Raphael-Boichot/Game_Boy_Mini_Flashable_Camera/Images/Artifacts_with_22pf_C10.png

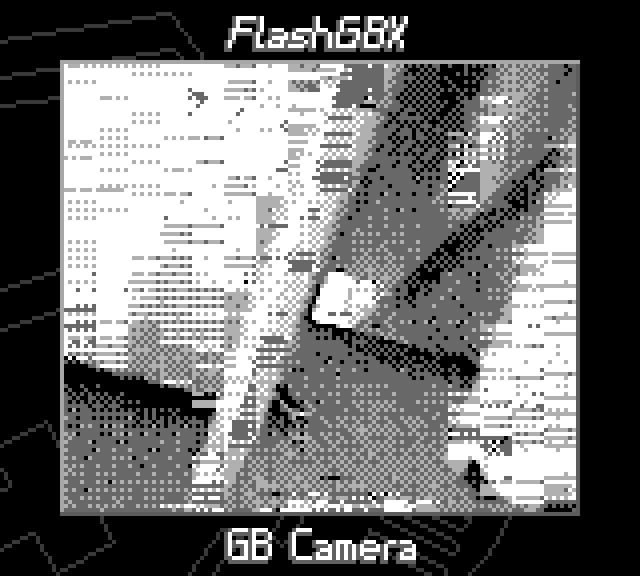
Images/Artifacts_with_22pf_C10.png
