Raphael-Boichot/Game_Boy_Mini_Flashable_Camera/PCB/GBC.kicad_sch

## KiCad design PCB/GBC.kicad_sch (2024-08-07)

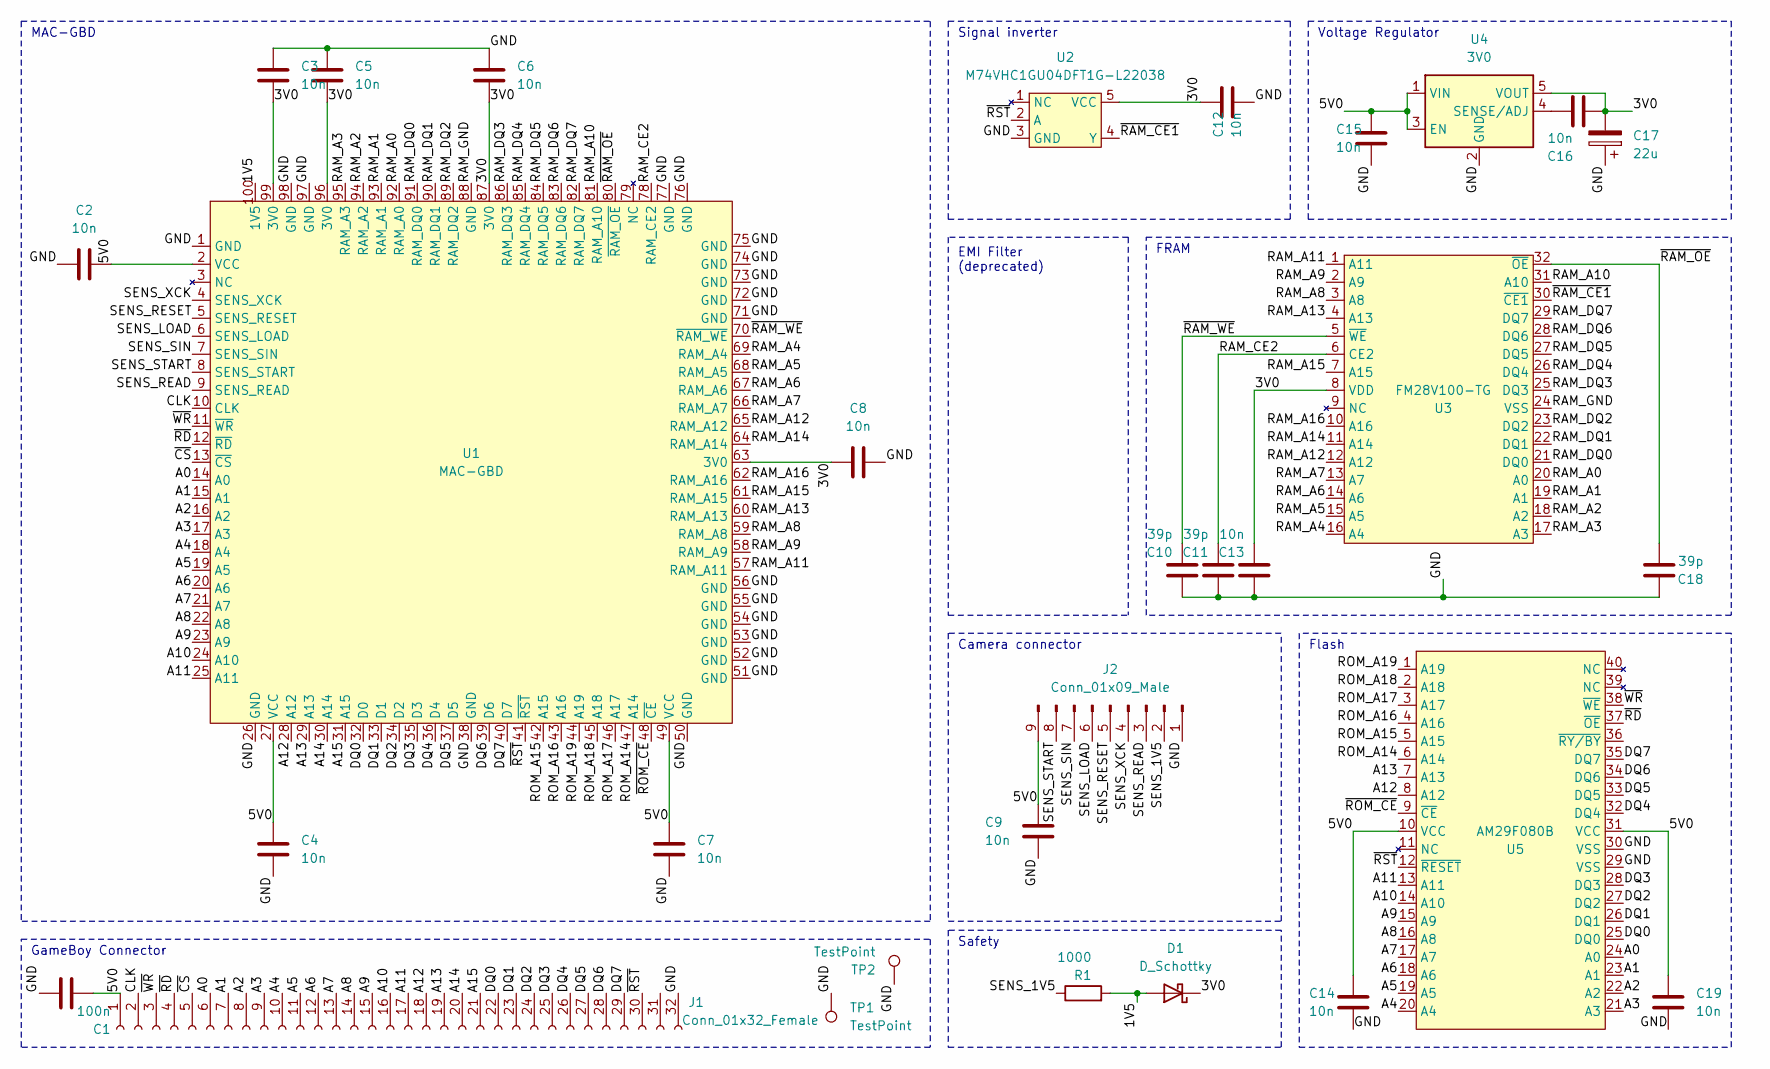
[picture p32: schematic GBC.kicad_sch]

Parts:
C1: 100n; C_0603_1608Metric
C2, C3, C4, C5, C6, C7, C8, C9, C12, C13, C14, C15, C16, C19: 10n; C_0603_1608Metric
C10, C11, C18: 39p; C_0603_1608Metric
C17: 22u; C_1206_3216Metric
D1: D_Schottky; Diode
J1: Conn_01x32_Female; Gamecart
J2: Conn_01x09_Male; JST_B9B-ZR-SM4-Flat
R1: 1000; R_0603_1608Metric
TP1, TP2: TestPoint; TestPoint_THTPad_D1.5mm_Drill0.7mm
U1: MAC-GBD; TQFP-100_14x14mm_P0.5mm
U2: M74VHC1GU04DFT1G-L22038; SC-88A
U3: FM28V100-TG; TSOP-I-32_12.4x8mm_P0.5mm
U4: 3V0; SOT-23-5_HandSoldering
U5: AM29F080B; TSOP-I-40_18.4x10mm_P0.5mm

Connections:
1V5: D1.2 (A), R1.2, U1.100 (1V5)
3V0: C3.1, C5.1, C6.1, C8.1, C12.1, C13.2, C16.2, C17.2, D1.1 (K), U1.63 (3V0), U1.87 (3V0), U1.96 (3V0), U1.99 (3V0), U2.5 (VCC), U3.8 (VDD), U4.5 (VOUT)
5V0: C1.1, C2.2, C4.1, C7.1, C9.2, C14.2, C15.1, C19.1, J1.1, J2.9, U1.2 (VCC), U1.27 (VCC), U1.49 (VCC), U4.1 (VIN), U4.3 (EN), U5.10 (VCC), U5.31 (VCC)
A0: J1.6, U1.14 (A0), U5.24 (A0)
A1: J1.7, U1.15 (A1), U5.23 (A1)
A2: J1.8, U1.16 (A2), U5.22 (A2)
A3: J1.9, U1.17 (A3), U5.21 (A3)
A4: J1.10, U1.18 (A4), U5.20 (A4)
A5: J1.11, U1.19 (A5), U5.19 (A5)
A6: J1.12, U1.20 (A6), U5.18 (A6)
A7: J1.13, U1.21 (A7), U5.17 (A7)
A8: J1.14, U1.22 (A8), U5.16 (A8)
A9: J1.15, U1.23 (A9), U5.15 (A9)
A10: J1.16, U1.24 (A10), U5.14 (A10)
A11: J1.17, U1.25 (A11), U5.13 (A11)
A12: J1.18, U1.28 (A12), U5.8 (A12)
A13: J1.19, U1.29 (A13), U5.7 (A13)
A14: J1.20, U1.30 (A14)
A15: J1.21, U1.31 (A15)
CLK: J1.2, U1.10 (CLK)
DQ0: J1.22, U1.32 (D0), U5.25 (DQ0)
DQ1: J1.23, U1.33 (D1), U5.26 (DQ1)
DQ2: J1.24, U1.34 (D2), U5.27 (DQ2)
DQ3: J1.25, U1.35 (D3), U5.28 (DQ3)
DQ4: J1.26, U1.36 (D4), U5.32 (DQ4)
DQ5: J1.27, U1.37 (D5), U5.33 (DQ5)
DQ6: J1.28, U1.39 (D6), U5.34 (DQ6)
DQ7: J1.29, U1.40 (D7), U5.35 (DQ7)
GND: C1.2, C2.1, C3.2, C4.2, C5.2, C6.2, C7.2, C8.2, C9.1, C10.1, C11.1, C12.2, C13.1, C14.1, C15.2, C17.1, C18.1, C19.2, J1.32, J2.1, TP1.1, TP2.1, U1.1 (GND), U1.26 (GND), U1.38 (GND), U1.50 (GND), U1.51 (GND), U1.52 (GND), U1.53 (GND), U1.54 (GND), U1.55 (GND), U1.56 (GND), U1.71 (GND), U1.72 (GND), U1.73 (GND), U1.74 (GND), U1.75 (GND), U1.76 (GND), U1.77 (GND), U1.97 (GND), U1.98 (GND), U2.3 (GND), U4.2 (GND), U5.29 (VSS), U5.30 (VSS)
unnamed: C16.1, U4.4 (SENSE/ADJ)
RAM_A0: U1.92 (RAM_A0), U3.20 (A0)
RAM_A1: U1.93 (RAM_A1), U3.19 (A1)
RAM_A2: U1.94 (RAM_A2), U3.18 (A2)
RAM_A3: U1.95 (RAM_A3), U3.17 (A3)
RAM_A4: U1.69 (RAM_A4), U3.16 (A4)
RAM_A5: U1.68 (RAM_A5), U3.15 (A5)
RAM_A6: U1.67 (RAM_A6), U3.14 (A6)
RAM_A7: U1.66 (RAM_A7), U3.13 (A7)
RAM_A8: U1.59 (RAM_A8), U3.3 (A8)
RAM_A9: U1.58 (RAM_A9), U3.2 (A9)
RAM_A10: U1.81 (RAM_A10), U3.31 (A10)
RAM_A11: U1.57 (RAM_A11), U3.1 (A11)
RAM_A12: U1.65 (RAM_A12), U3.12 (A12)
RAM_A13: U1.60 (RAM_A13), U3.4 (A13)
RAM_A14: U1.64 (RAM_A14), U3.11 (A14)
RAM_A15: U1.61 (RAM_A15), U3.7 (A15)
RAM_A16: U1.62 (RAM_A16), U3.10 (A16)
RAM_CE2: C11.2, U1.78 (RAM_CE2), U3.6 (CE2)
RAM_DQ0: U1.91 (RAM_DQ0), U3.21 (DQ0)
RAM_DQ1: U1.90 (RAM_DQ1), U3.22 (DQ1)
RAM_DQ2: U1.89 (RAM_DQ2), U3.23 (DQ2)
RAM_DQ3: U1.86 (RAM_DQ3), U3.25 (DQ3)
RAM_DQ4: U1.85 (RAM_DQ4), U3.26 (DQ4)
RAM_DQ5: U1.84 (RAM_DQ5), U3.27 (DQ5)
RAM_DQ6: U1.83 (RAM_DQ6), U3.28 (DQ6)
RAM_DQ7: U1.82 (RAM_DQ7), U3.29 (DQ7)
RAM_GND: U1.88 (GND), U3.24 (VSS)
ROM_A14: U1.47 (A14), U5.6 (A14)
ROM_A15: U1.42 (A15), U5.5 (A15)
ROM_A16: U1.43 (A16), U5.4 (A16)
ROM_A17: U1.46 (A17), U5.3 (A17)
ROM_A18: U1.45 (A18), U5.2 (A18)
ROM_A19: U1.44 (A19), U5.1 (A19)
SENS_1V5: J2.2, R1.1
SENS_LOAD: J2.6, U1.6 (SENS_LOAD)
SENS_READ: J2.3, U1.9 (SENS_READ)
SENS_RESET: J2.5, U1.5 (SENS_RESET)
SENS_SIN: J2.7, U1.7 (SENS_SIN)
SENS_START: J2.8, U1.8 (SENS_START)
SENS_XCK: J2.4, U1.4 (SENS_XCK)
~CS: J1.5, U1.13 (~CS)
~RAM_CE1: U2.4 (Y), U3.30 (~CE1)
~RAM_OE: C18.2, U1.80 (~RAM_OE), U3.32 (~OE)
~RAM_WE: C10.2, U1.70 (~RAM_WE), U3.5 (~WE)
~RD: J1.4, U1.12 (~RD), U5.37 (~OE)
~ROM_CE: U1.48 (~CE), U5.9 (~CE)
~RST: J1.30, U1.41 (~RST), U2.2 (A), U5.12 (~RESET)
~WR: J1.3, U1.11 (~WR), U5.38 (~WE)

Notes on the sheet:
Camera connector
Signal inverter
Flash
MAC-GBD
GameBoy Connector
FRAM
Voltage Regulator
EMI Filter (deprecated)
Safety
